JackelLab/CorsaOBDGauge/Firmware/TFT_eSPI/User_Setups/Setup204_ST7735_160x80.h

// ST7789 160 x 80 display with no chip select line
#define USER_SETUP_ID 204

#define ST7735_DRIVER

#define TFT_HEIGHT 160
#define TFT_WIDTH  80

#define ST7735_GREENTAB160x80

//#define TFT_RGB_ORDER TFT_RGB  // Colour order Red-Green-Blue
//#define TFT_RGB_ORDER TFT_BGR  // Colour order Blue-Green-Red

#define TFT_MOSI 23 // In some display driver board, it might be written as "SDA" and so on.
#define TFT_SCLK 18
#define TFT_CS   5  // Chip select control pin
#define TFT_DC   4  // Data Command control pin
#define TFT_RST  15  // Reset pin (could connect to Arduino RESET pin)
#define TFT_BL   2  // LED back-light

#define LOAD_GLCD   // Font 1. Original Adafruit 8 pixel font needs ~1820 bytes in FLASH
#define LOAD_FONT2  // Font 2. Small 16 pixel high font, needs ~3534 bytes in FLASH, 96 characters
#define LOAD_FONT4  // Font 4. Medium 26 pixel high font, needs ~5848 bytes in FLASH, 96 characters
#define LOAD_FONT6  // Font 6. Large 48 pixel font, needs ~2666 bytes in FLASH, only characters 1234567890:-.apm
#define LOAD_FONT7  // Font 7. 7 segment 48 pixel font, needs ~2438 bytes in FLASH, only characters 1234567890:.
#define LOAD_FONT8  // Font 8. Large 75 pixel font needs ~3256 bytes in FLASH, only characters 1234567890:-.
//#define LOAD_FONT8N // Font 8. Alternative to Font 8 above, slightly narrower, so 3 digits fit a 160 pixel TFT
#define LOAD_GFXFF  // FreeFonts. Include access to the 48 Adafruit_GFX free fonts FF1 to FF48 and custom fonts

#define SMOOTH_FONT


#define SPI_FREQUENCY  27000000
